jonnor/toothbrush/doc/img/toothbrush-3dmodel.png

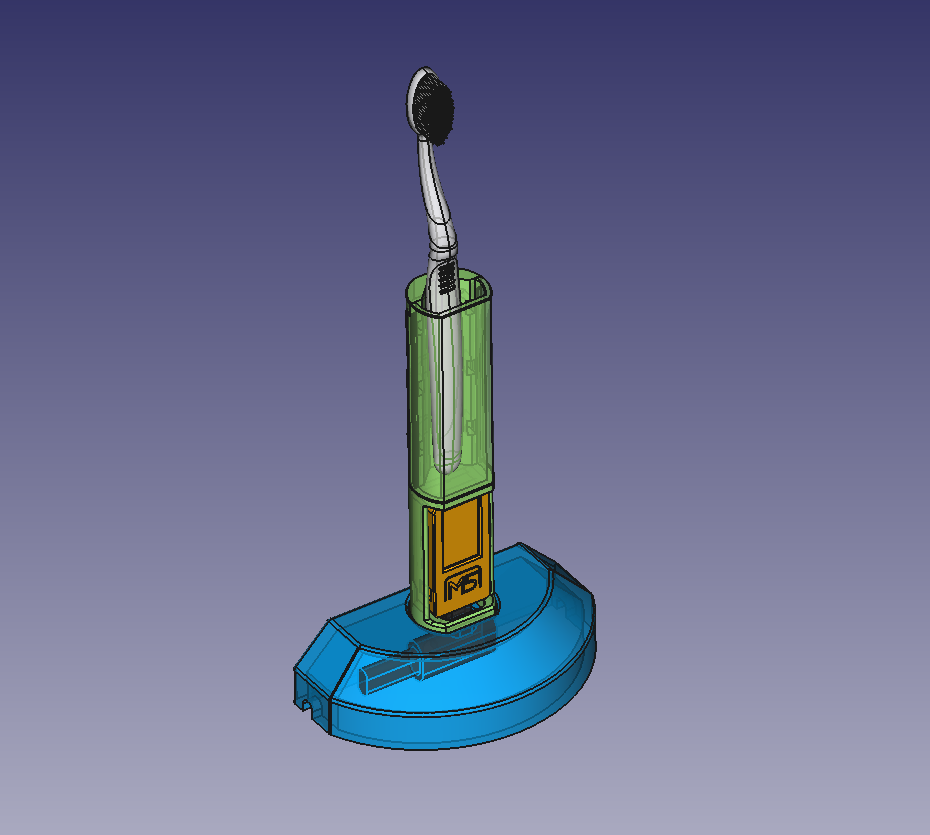
doc/img/toothbrush-3dmodel.png
