jonnor/toothbrush/doc/img/toothbrush-3dmodel_crop.png

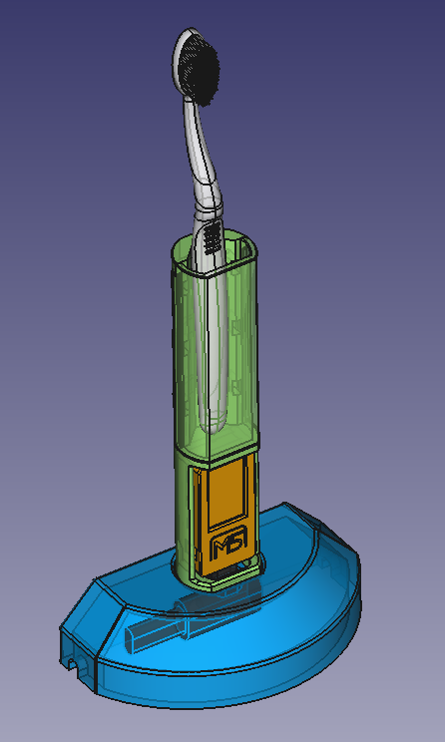
doc/img/toothbrush-3dmodel_crop.png
