jonnor/toothbrush/doc/img/toothbrush-data-flow.png

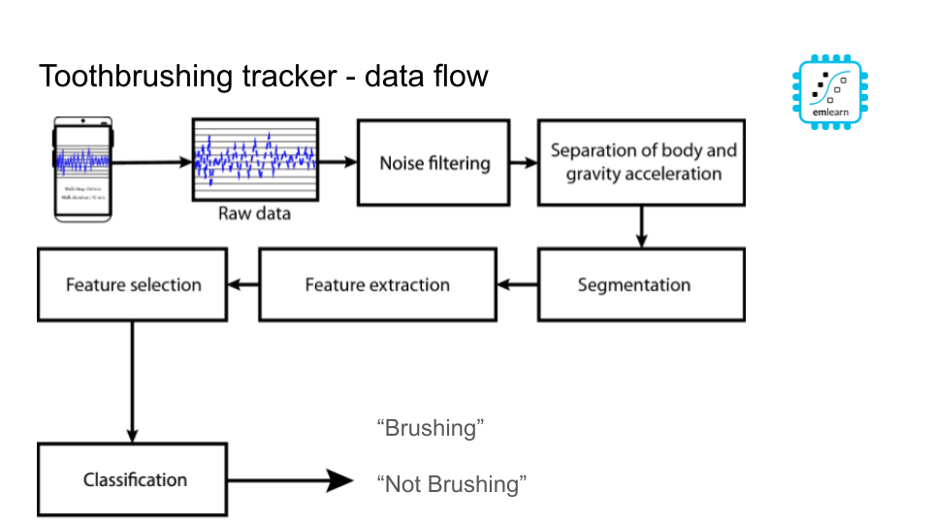
doc/img/toothbrush-data-flow.png
