jonnor/toothbrush/doc/img/toothbrush-onepage-43.png

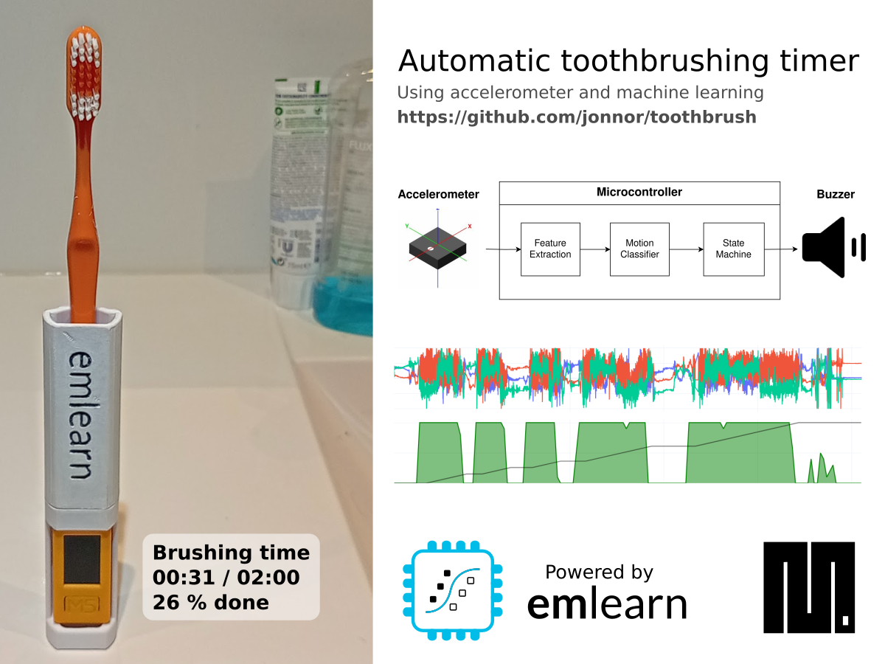
doc/img/toothbrush-onepage-43.png
