jonnor/toothbrush/doc/img/toothbrush-timeline.png

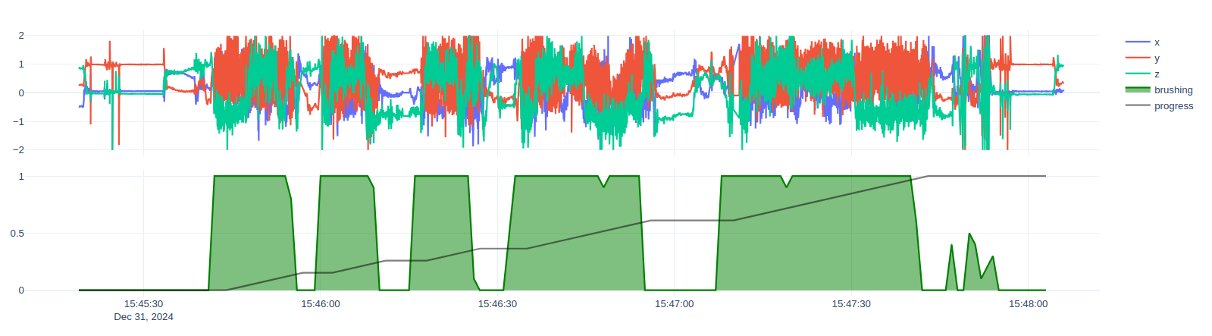
doc/img/toothbrush-timeline.png
