jonnor/toothbrush/doc/img/toothbrush-parts.jpg

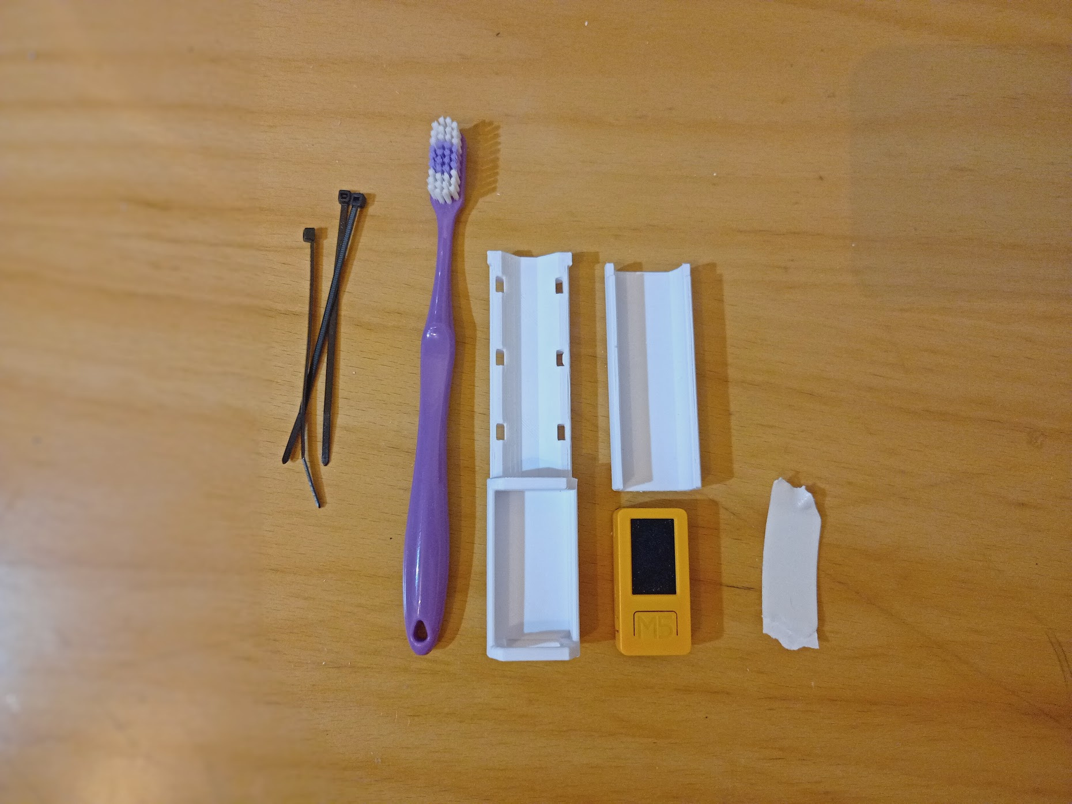
doc/img/toothbrush-parts.jpg
